Bastineitor73/Biped-Robot/Software y Comunicación/README.md

# Software B1P0

## Rutina principal
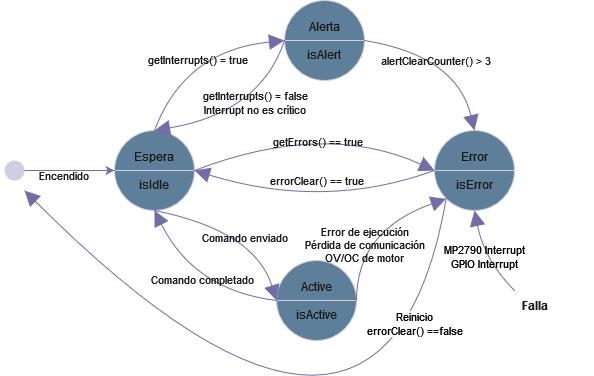
[picture p78: Software y Comunicación/Diagrama_FSM.drawio.png]


## Libreria MP2790
- 144 Direcciones en #define
- 597 Registros en Namespace::MP2790_Reg con tipo struct RegDes
- 24 Metodos publicos
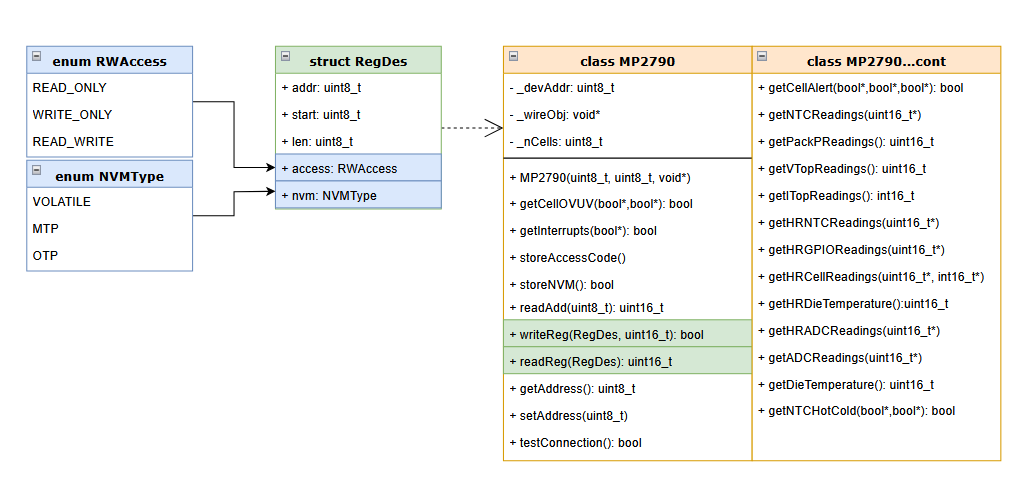
[picture p79: Software y Comunicación/Librerías Arduino/MP27XX/mp2790_class.png]
