Bastineitor73/Biped-Robot/Electrónica/PCB/Prototype1.0/Captura de pantalla 2025-07-23 153957.png

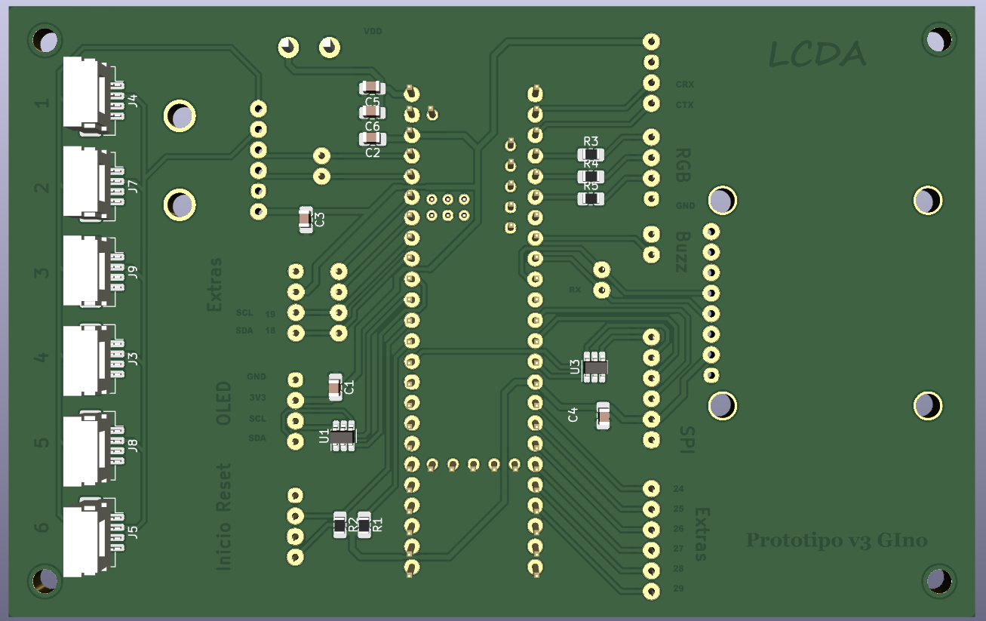
Electrónica/PCB/Prototype1.0/Captura de pantalla 2025-07-23 153957.png
