Bastineitor73/Biped-Robot/invitacion_1.jpg

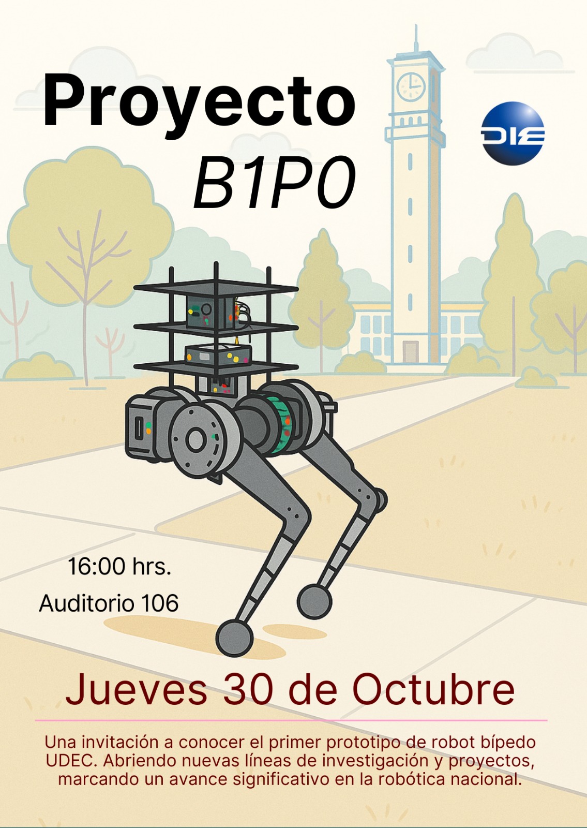
invitacion_1.jpg
