Bastineitor73/Biped-Robot/invitacion_2.png

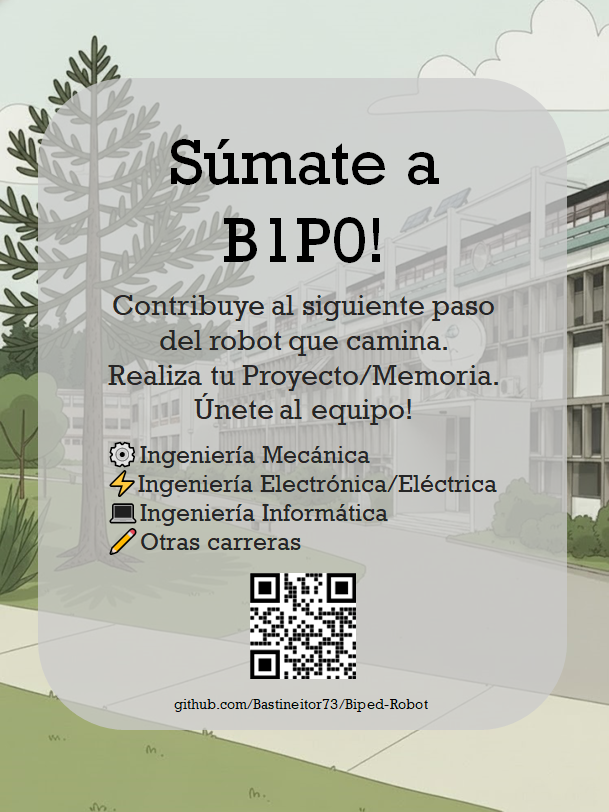
invitacion_2.png
