Bastineitor73/Biped-Robot/Software y Comunicación/Cámara/librealsense/doc/img/ds5_branches.png

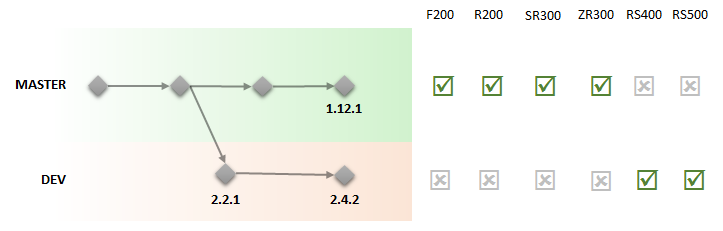
Software y Comunicación/Cámara/librealsense/doc/img/ds5_branches.png
