Bastineitor73/Biped-Robot/Software y Comunicación/Cámara/librealsense/doc/img/LRS_CS_axis_base.png

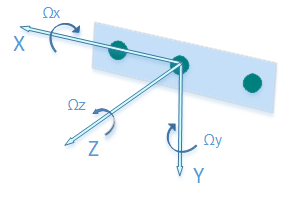
Software y Comunicación/Cámara/librealsense/doc/img/LRS_CS_axis_base.png
