Bastineitor73/Biped-Robot/Software y Comunicación/Cámara/librealsense/doc/img/matlab_select.png

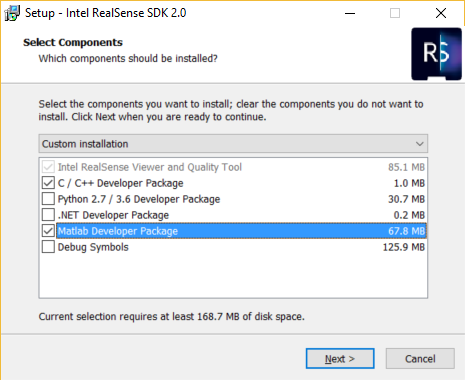
Software y Comunicación/Cámara/librealsense/doc/img/matlab_select.png
