Bastineitor73/Biped-Robot/Software y Comunicación/Cámara/librealsense/doc/img/playback/playback-flow.png

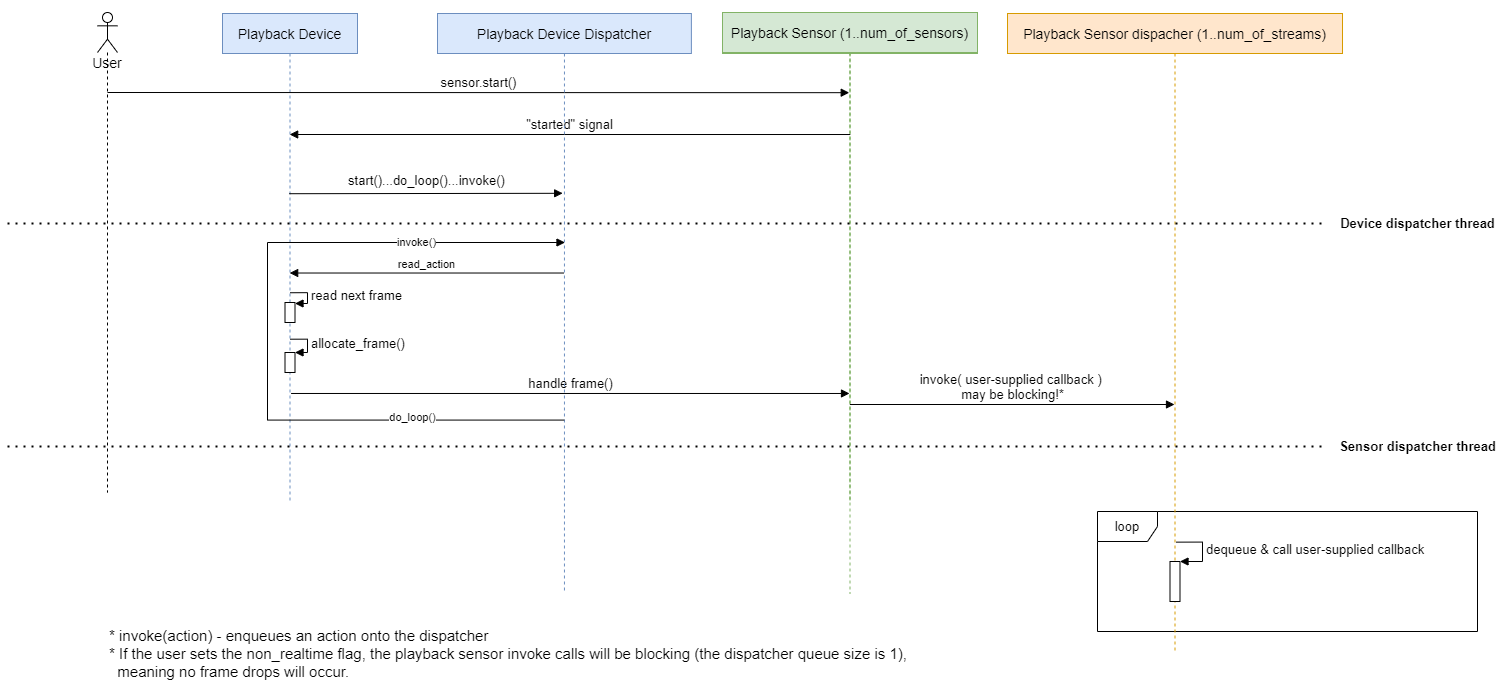
Software y Comunicación/Cámara/librealsense/doc/img/playback/playback-flow.png
