Bastineitor73/Biped-Robot/Software y Comunicación/Cámara/librealsense/doc/img/playback_screenshot.png

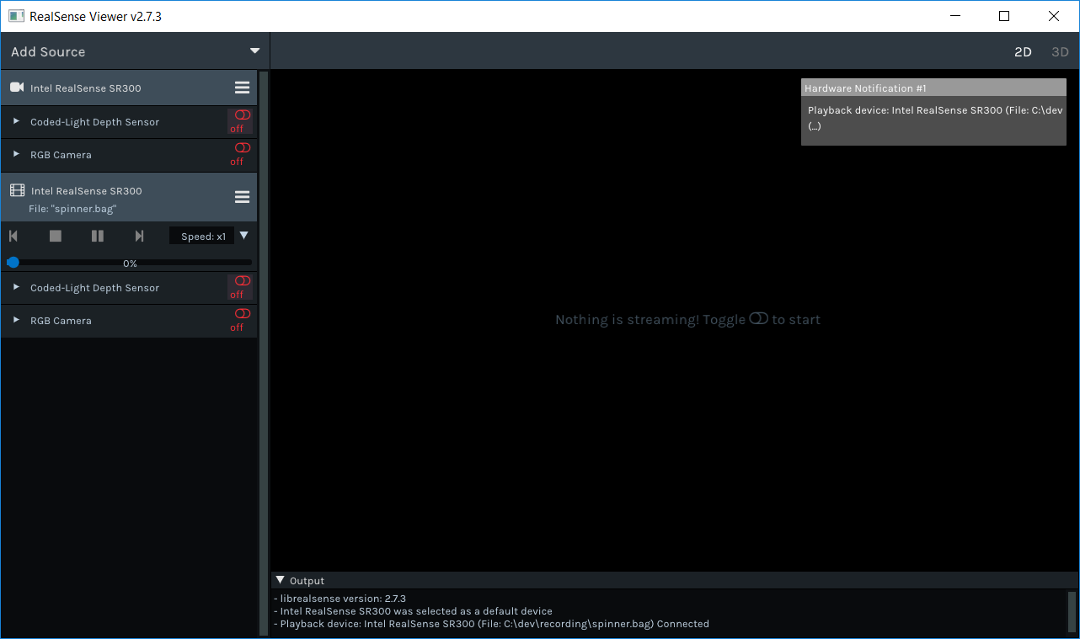
Software y Comunicación/Cámara/librealsense/doc/img/playback_screenshot.png
