Bastineitor73/Biped-Robot/Software y Comunicación/Cámara/librealsense/doc/img/realsense-android.png

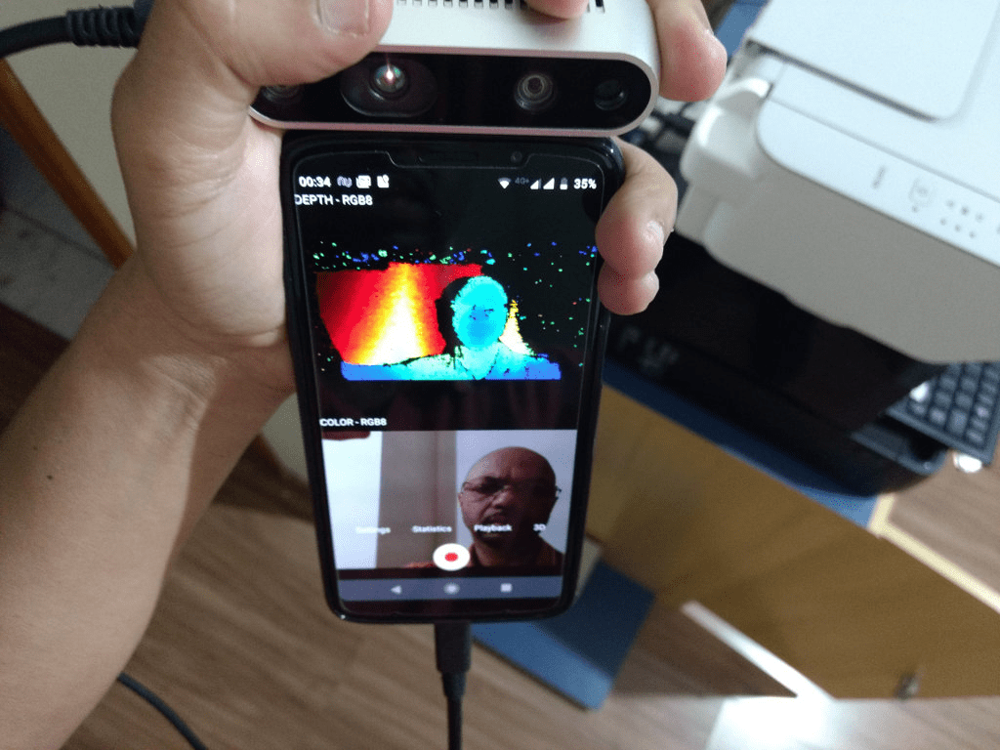
Software y Comunicación/Cámara/librealsense/doc/img/realsense-android.png
