Bastineitor73/Biped-Robot/Software y Comunicación/Cámara/librealsense/doc/img/record_screenshot.png

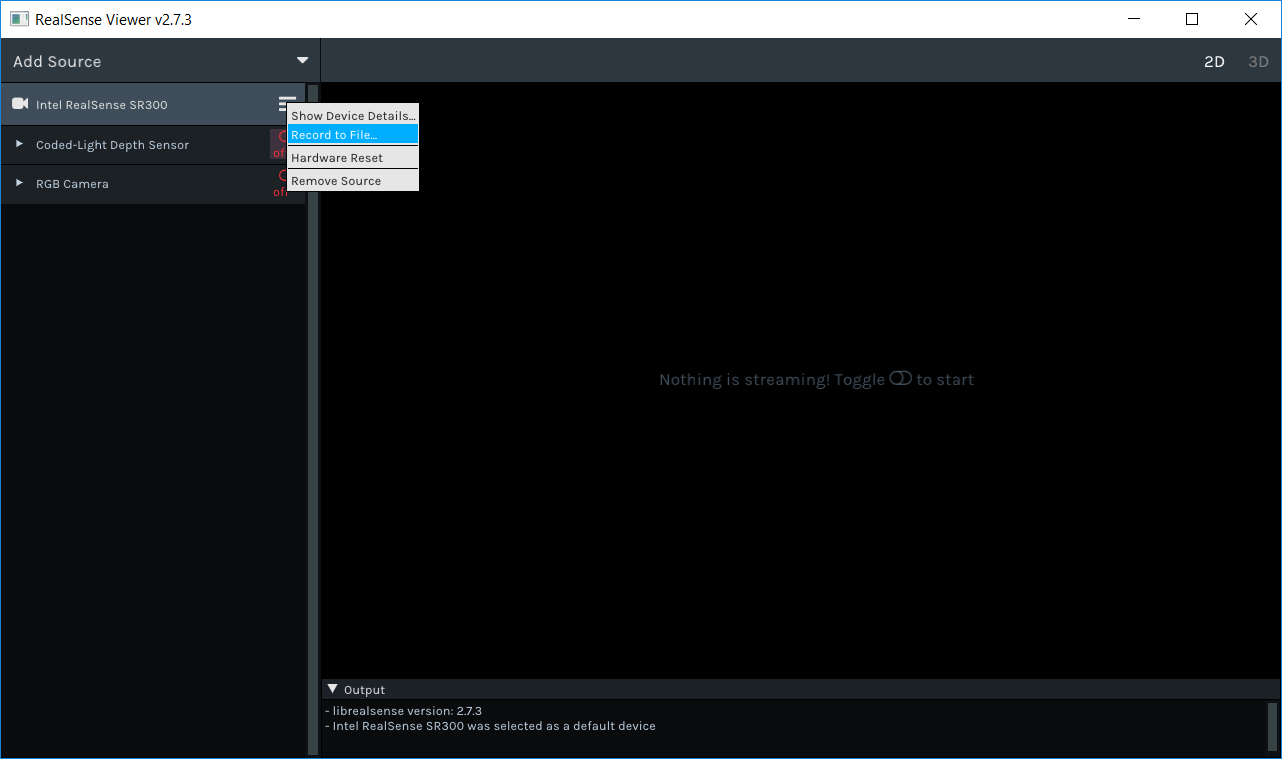
Software y Comunicación/Cámara/librealsense/doc/img/record_screenshot.png
