Bastineitor73/Biped-Robot/Software y Comunicación/Cámara/librealsense/doc/img/sensors_within_device.png

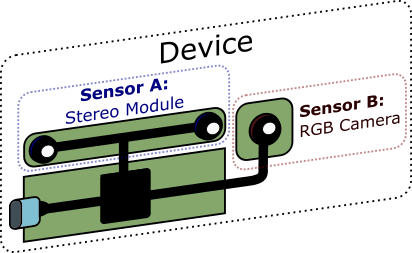
Software y Comunicación/Cámara/librealsense/doc/img/sensors_within_device.png
