Bastineitor73/Biped-Robot/Software y Comunicación/Cámara/librealsense/doc/img/T265_orientation_axis.png

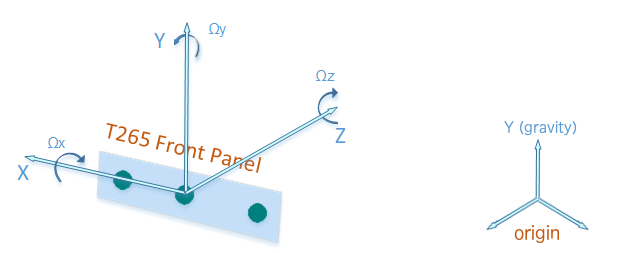
Software y Comunicación/Cámara/librealsense/doc/img/T265_orientation_axis.png
