Bastineitor73/Biped-Robot/Software y Comunicación/Cámara/librealsense/doc/img/T265_Robot1.png

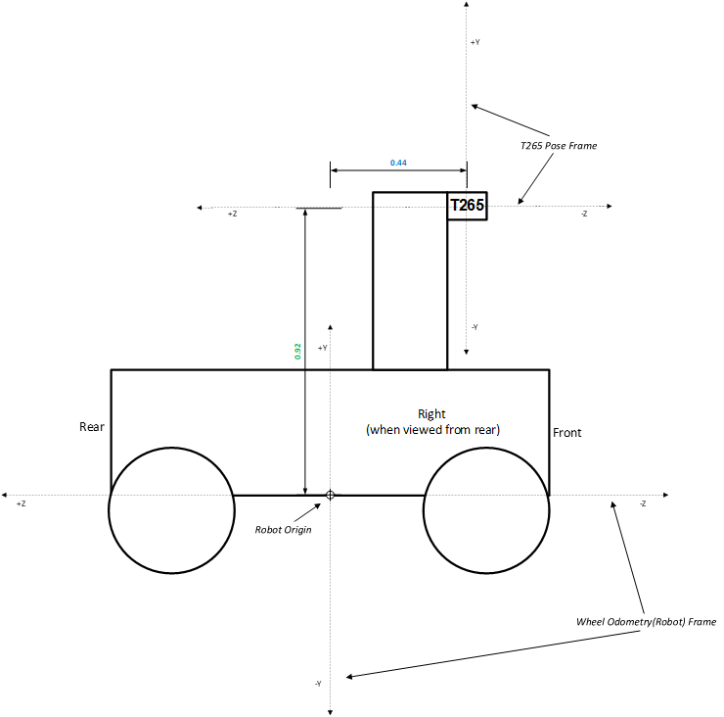
Software y Comunicación/Cámara/librealsense/doc/img/T265_Robot1.png
