Bastineitor73/Biped-Robot/Software y Comunicación/Cámara/librealsense/doc/img/T265_sensor_extrinsics.png

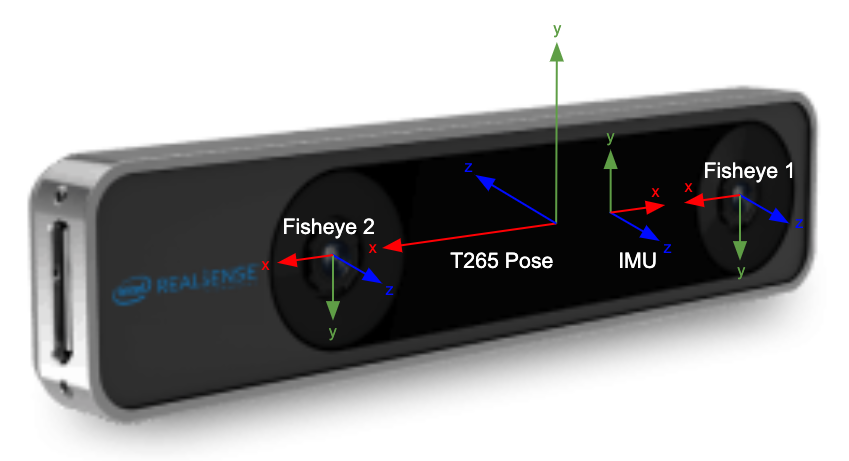
Software y Comunicación/Cámara/librealsense/doc/img/T265_sensor_extrinsics.png
