Bastineitor73/Biped-Robot/Software y Comunicación/Cámara/librealsense/doc/img/updates/updates.png

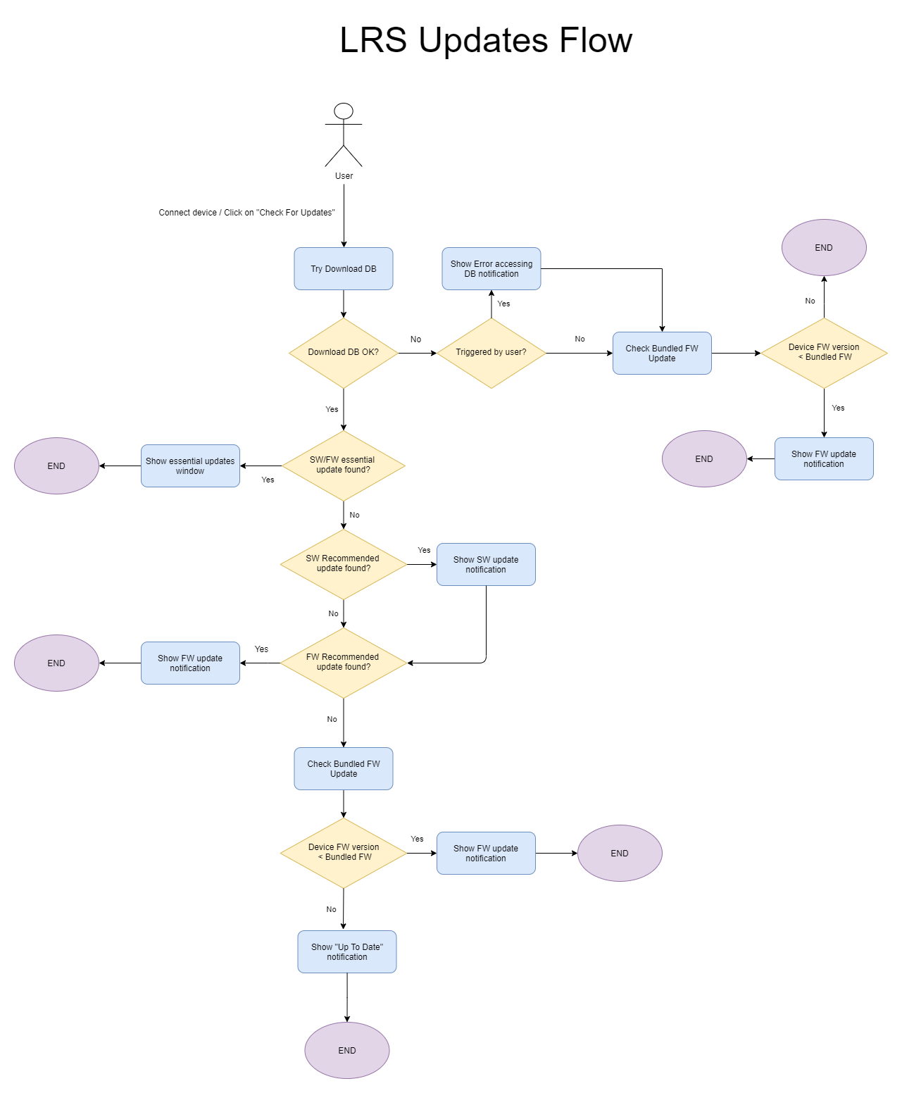
Software y Comunicación/Cámara/librealsense/doc/img/updates/updates.png
