Bastineitor73/Biped-Robot/Software y Comunicación/Cámara/librealsense/doc/img/win_samples.PNG

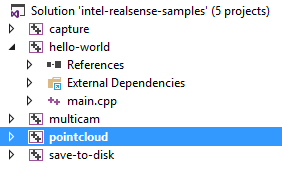
Software y Comunicación/Cámara/librealsense/doc/img/win_samples.PNG
