Bastineitor73/Biped-Robot/Software y Comunicación/Cámara/librealsense/doc/img/win_shortcuts.PNG

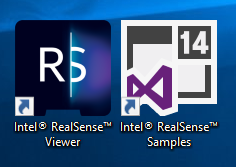
Software y Comunicación/Cámara/librealsense/doc/img/win_shortcuts.PNG
