Bastineitor73/Biped-Robot/Software y Comunicación/Cámara/librealsense/doc/img/windows_pointcloud_preview.PNG

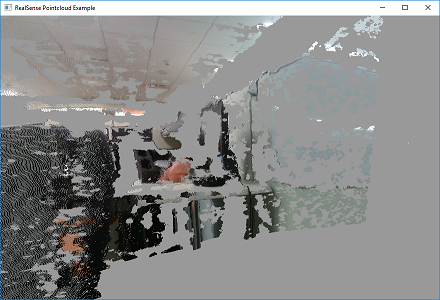
Software y Comunicación/Cámara/librealsense/doc/img/windows_pointcloud_preview.PNG
