Bastineitor73/Biped-Robot/Software y Comunicación/Cámara/librealsense/doc/img/windows_viewer_preview.PNG

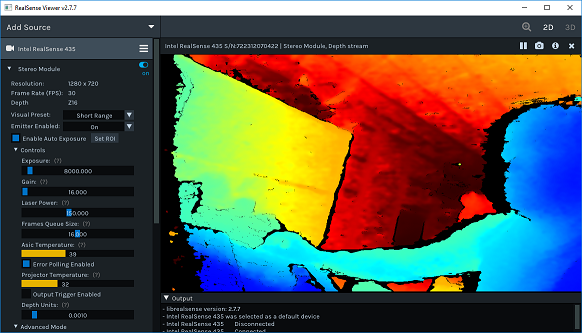
Software y Comunicación/Cámara/librealsense/doc/img/windows_viewer_preview.PNG
