Bastineitor73/Biped-Robot/Software y Comunicación/Cámara/librealsense/doc/metadata/metadata-cpp-config-ui.png

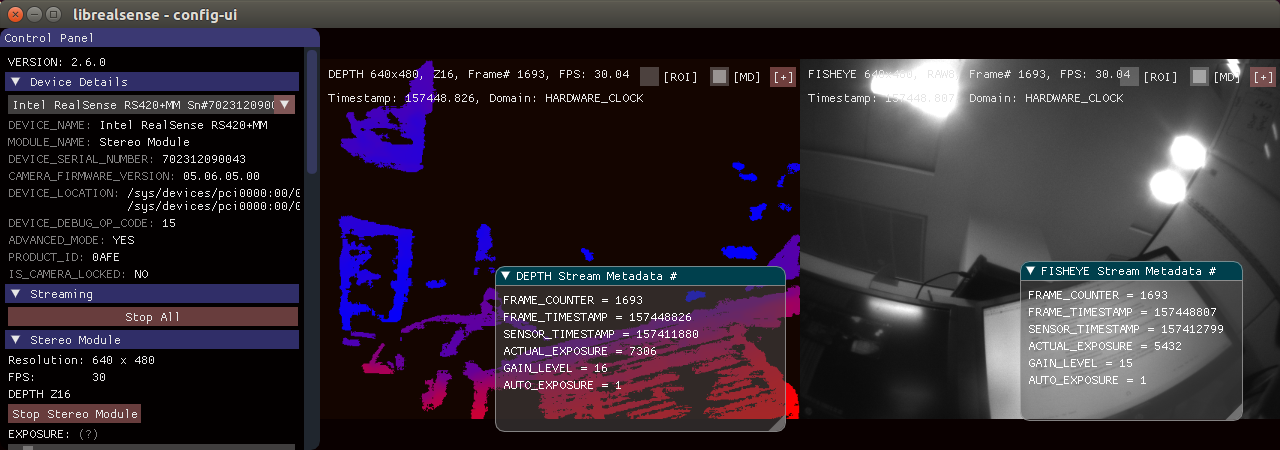
Software y Comunicación/Cámara/librealsense/doc/metadata/metadata-cpp-config-ui.png
