Bastineitor73/Biped-Robot/Software y Comunicación/Cámara/librealsense/doc/metadata/metadata_acquisition_flow.bmp

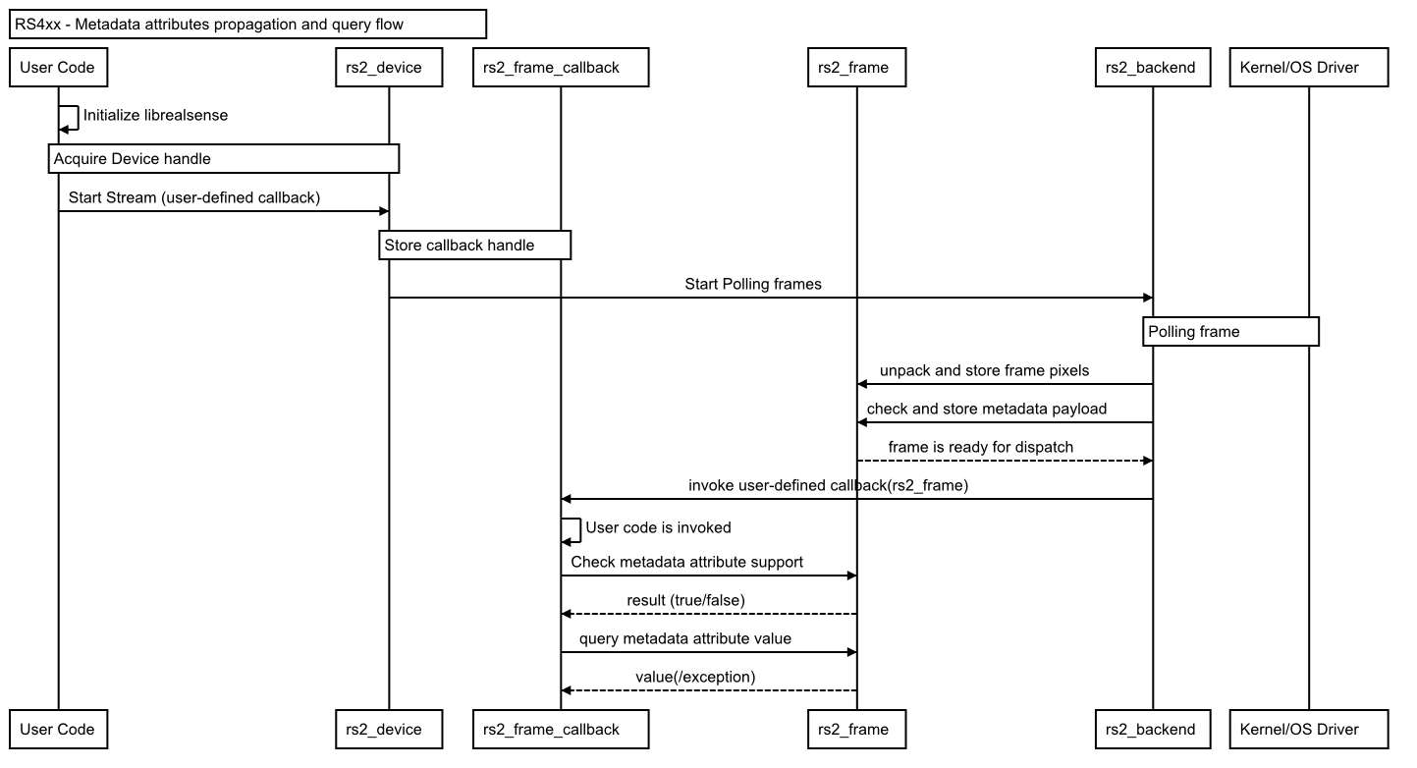
Software y Comunicación/Cámara/librealsense/doc/metadata/metadata_acquisition_flow.bmp
