Bastineitor73/Biped-Robot/Software y Comunicación/Cámara/librealsense/doc/metadata/metadata_registration_flow.bmp

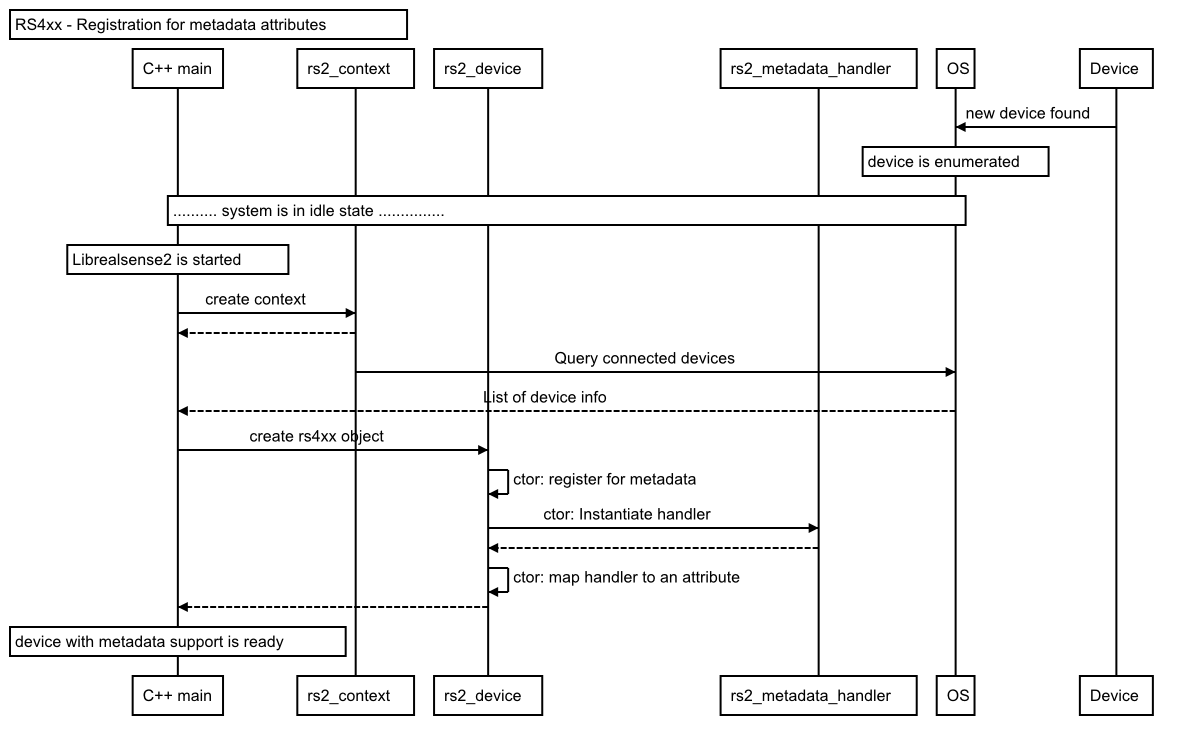
Software y Comunicación/Cámara/librealsense/doc/metadata/metadata_registration_flow.bmp
