Bastineitor73/Biped-Robot/Software y Comunicación/Cámara/librealsense/doc/rs400/advanced_mode_sample.png

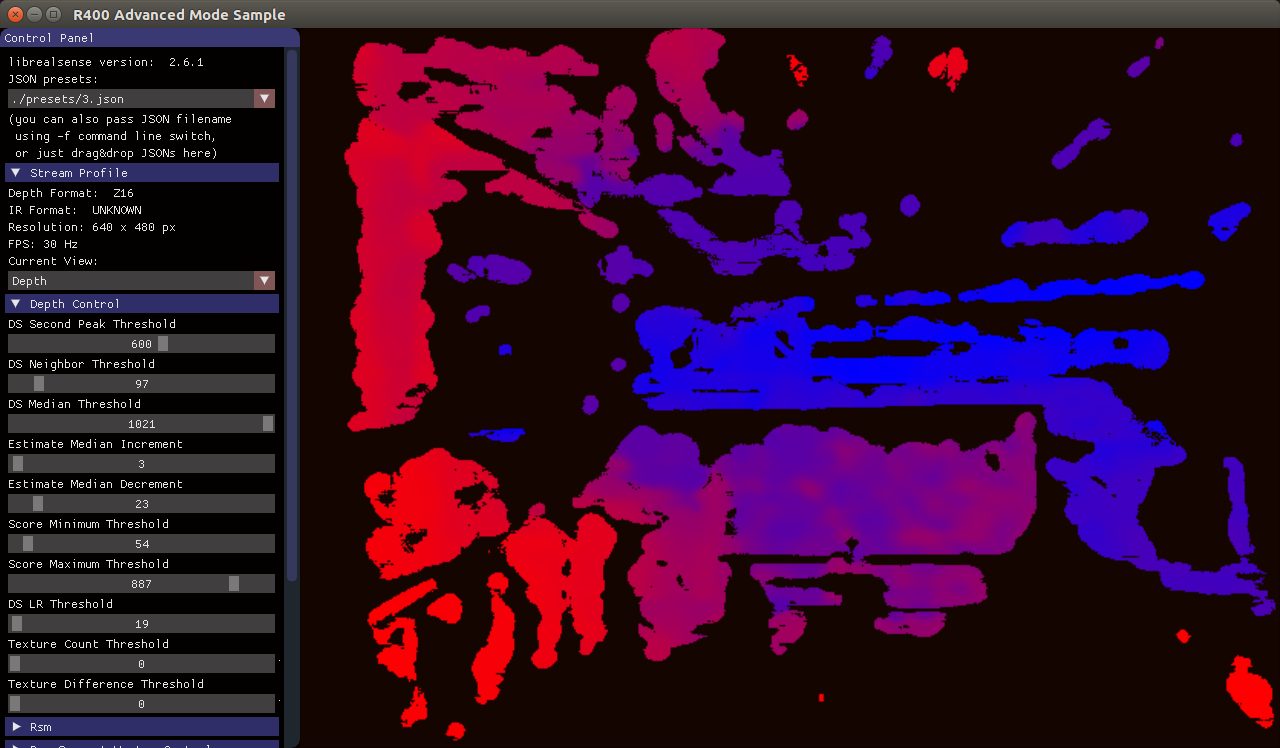
Software y Comunicación/Cámara/librealsense/doc/rs400/advanced_mode_sample.png
