Bastineitor73/Biped-Robot/Software y Comunicación/Cámara/librealsense/doc/stepbystep/resources/Image_Depth.png

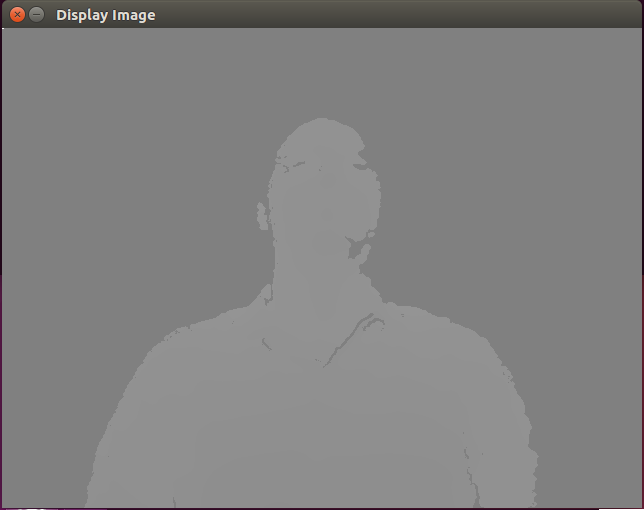
Software y Comunicación/Cámara/librealsense/doc/stepbystep/resources/Image_Depth.png
