Bastineitor73/Biped-Robot/Software y Comunicación/Cámara/librealsense/doc/stepbystep/resources/Image_IR-noColorMap.png

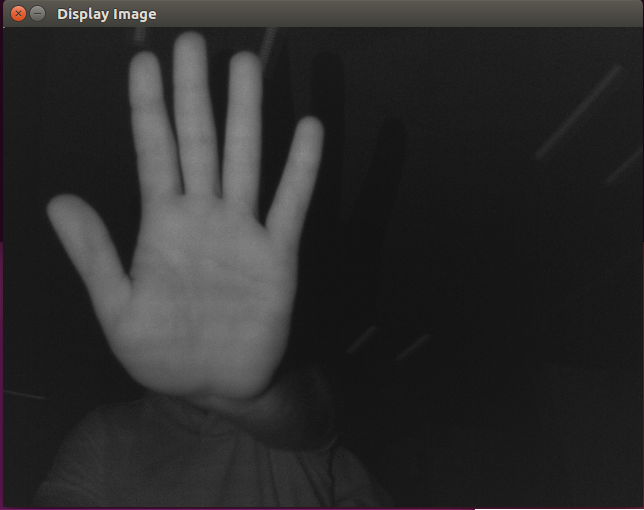
Software y Comunicación/Cámara/librealsense/doc/stepbystep/resources/Image_IR-noColorMap.png
