Bastineitor73/Biped-Robot/Software y Comunicación/Cámara/librealsense/examples/gl/output.PNG

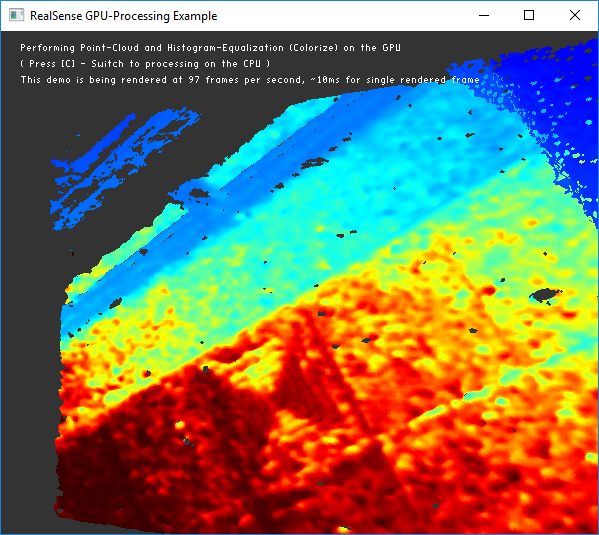
Software y Comunicación/Cámara/librealsense/examples/gl/output.PNG
