Bastineitor73/Biped-Robot/Software y Comunicación/Cámara/librealsense/scripts/Docker/LRS_Docker_Depth_example.gif

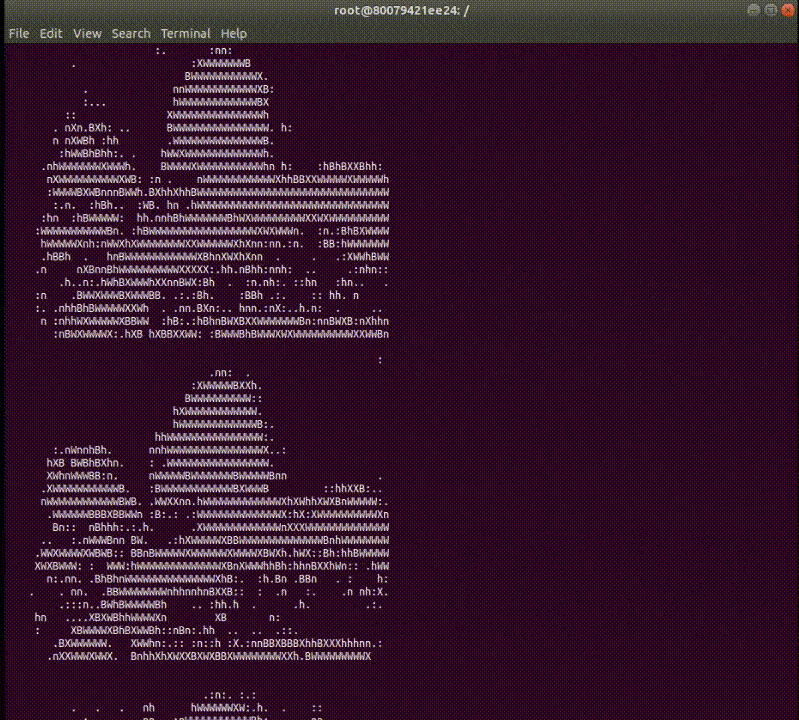
Software y Comunicación/Cámara/librealsense/scripts/Docker/LRS_Docker_Depth_example.gif
