Bastineitor73/Biped-Robot/Software y Comunicación/Cámara/librealsense/tools/depth-quality/res/z_accuracy.png

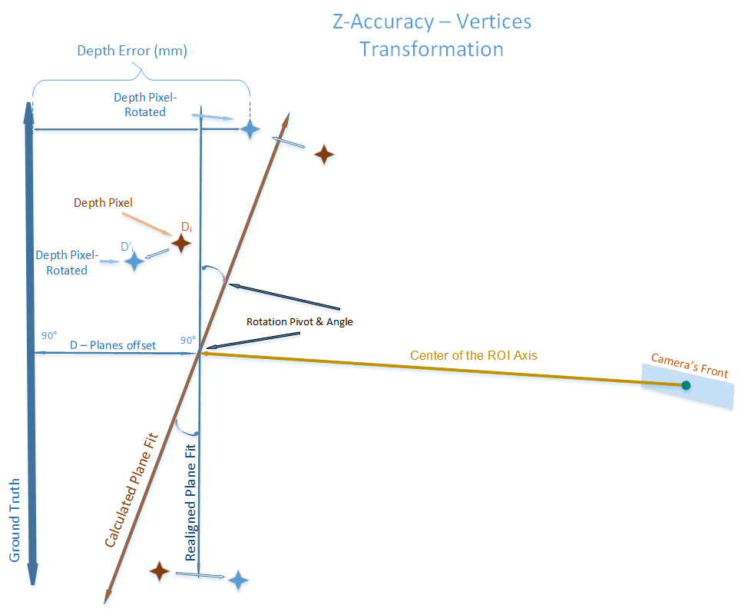
Software y Comunicación/Cámara/librealsense/tools/depth-quality/res/z_accuracy.png
