Bastineitor73/Biped-Robot/Software y Comunicación/Cámara/librealsense/tools/depth-quality/res/Zi_ZPi.png

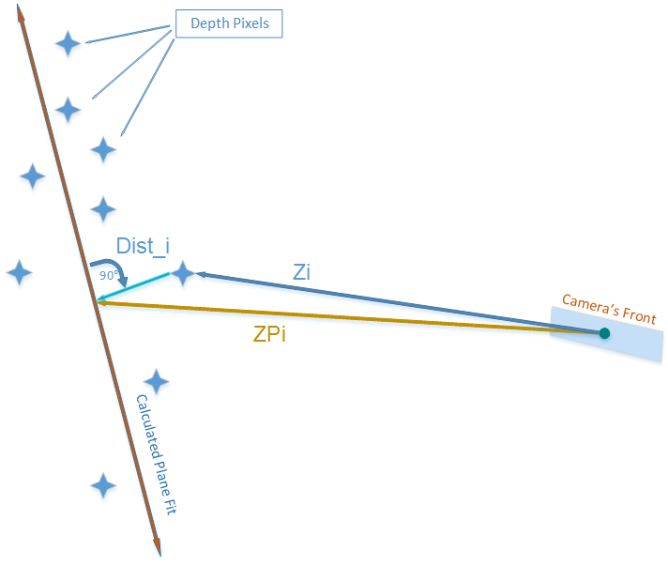
Software y Comunicación/Cámara/librealsense/tools/depth-quality/res/Zi_ZPi.png
