Bastineitor73/Biped-Robot/Software y Comunicación/Cámara/librealsense/wrappers/dlib/face/rs-face-dlib.jpg

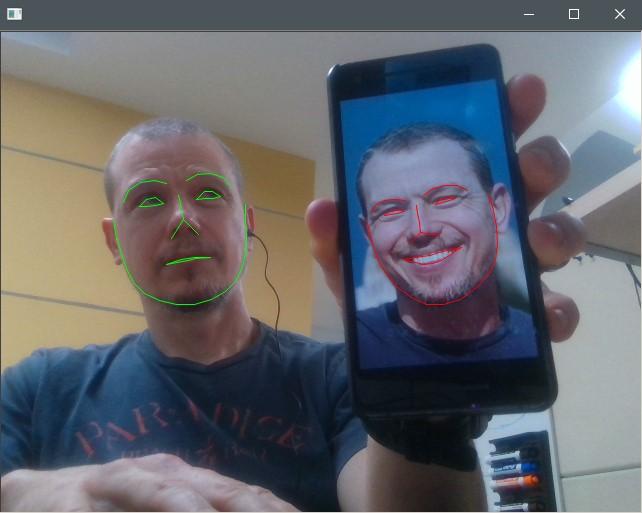
Software y Comunicación/Cámara/librealsense/wrappers/dlib/face/rs-face-dlib.jpg
