Bastineitor73/Biped-Robot/Software y Comunicación/Cámara/librealsense/wrappers/opencv/dnn/res/1.PNG

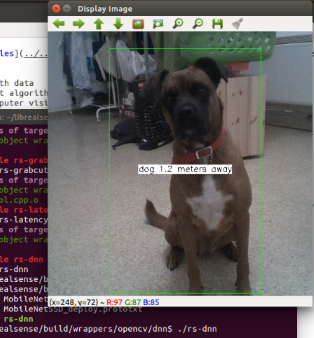
Software y Comunicación/Cámara/librealsense/wrappers/opencv/dnn/res/1.PNG
