Bastineitor73/Biped-Robot/Software y Comunicación/Cámara/librealsense/wrappers/opencv/grabcuts/res/input.png

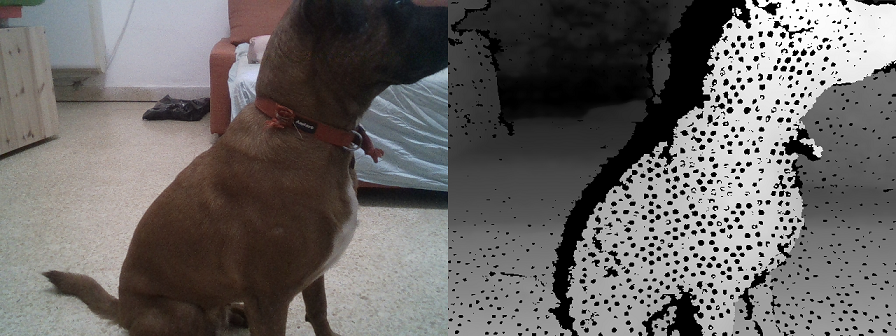
Software y Comunicación/Cámara/librealsense/wrappers/opencv/grabcuts/res/input.png
