Bastineitor73/Biped-Robot/Software y Comunicación/Cámara/librealsense/wrappers/opencv/grabcuts/res/masks.png

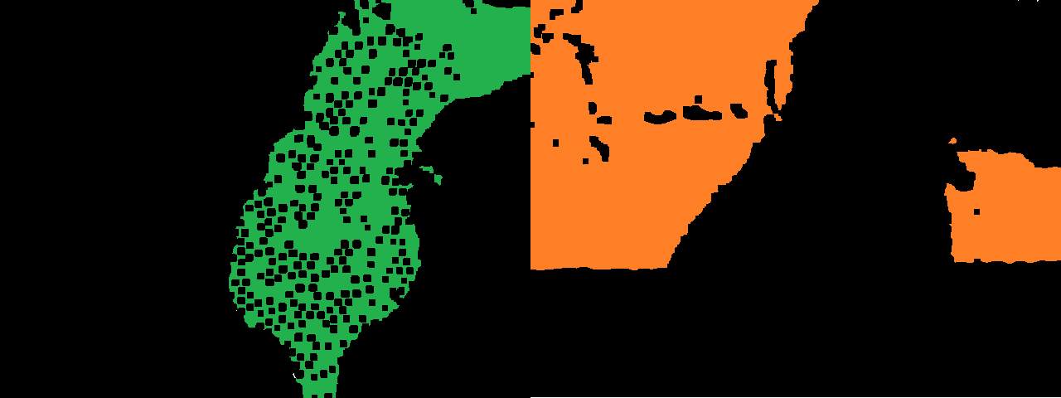
Software y Comunicación/Cámara/librealsense/wrappers/opencv/grabcuts/res/masks.png
