Bastineitor73/Biped-Robot/Software y Comunicación/Cámara/librealsense/wrappers/opencv/latency-tool/res/3.png

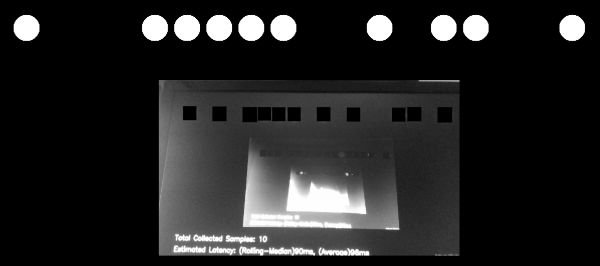
Software y Comunicación/Cámara/librealsense/wrappers/opencv/latency-tool/res/3.png
