Bastineitor73/Biped-Robot/Software y Comunicación/Cámara/librealsense/wrappers/opencv/res/4.PNG

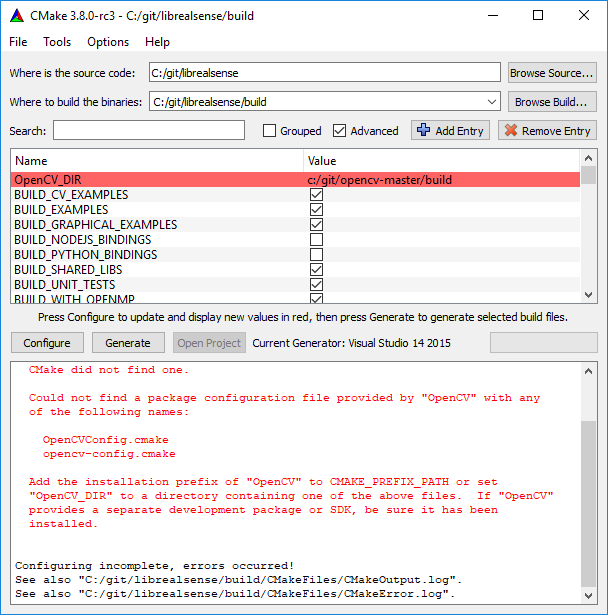
Software y Comunicación/Cámara/librealsense/wrappers/opencv/res/4.PNG
