Bastineitor73/Biped-Robot/Software y Comunicación/Cámara/librealsense/wrappers/opencv/rotate-pointcloud/res/front.png

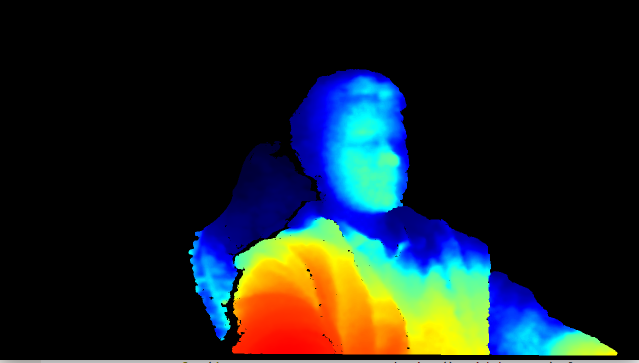
Software y Comunicación/Cámara/librealsense/wrappers/opencv/rotate-pointcloud/res/front.png
