Bastineitor73/Biped-Robot/Software y Comunicación/Cámara/librealsense/wrappers/opencv/rotate-pointcloud/res/roll_90.png

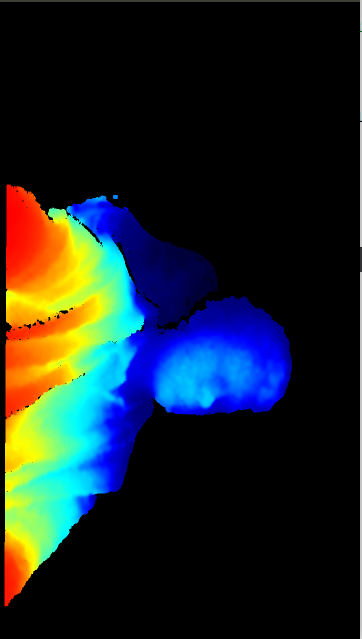
Software y Comunicación/Cámara/librealsense/wrappers/opencv/rotate-pointcloud/res/roll_90.png
