Bastineitor73/Biped-Robot/Software y Comunicación/Cámara/librealsense/wrappers/opencv/rotate-pointcloud/res/yaw_90.png

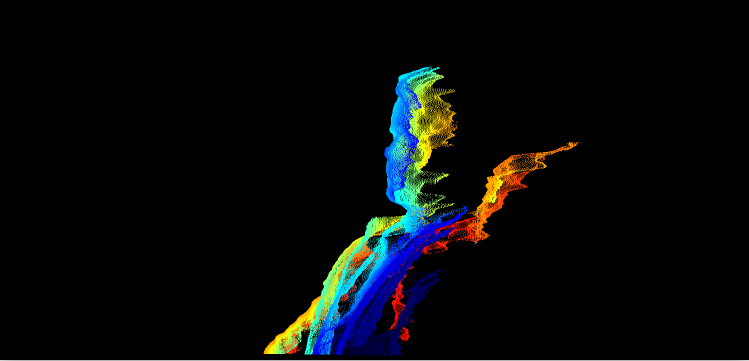
Software y Comunicación/Cámara/librealsense/wrappers/opencv/rotate-pointcloud/res/yaw_90.png
