Bastineitor73/Biped-Robot/Software y Comunicación/Cámara/librealsense/wrappers/openni2/doc/img/demo.jpg

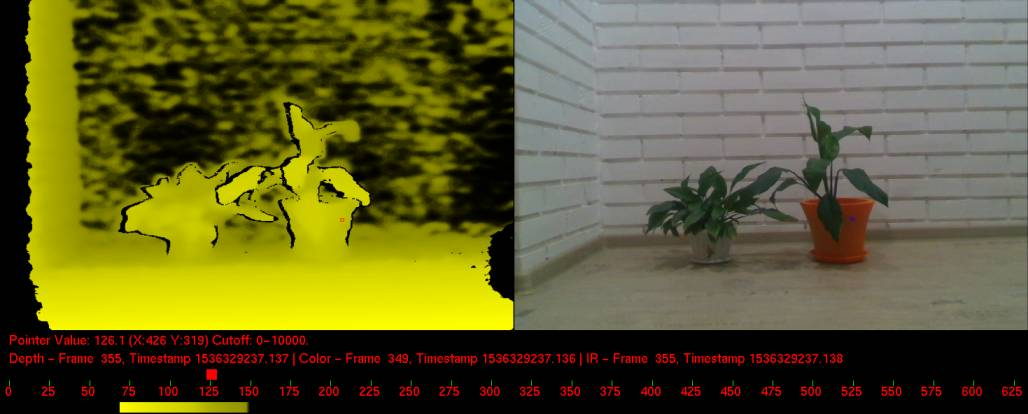
Software y Comunicación/Cámara/librealsense/wrappers/openni2/doc/img/demo.jpg
