Bastineitor73/Biped-Robot/Software y Comunicación/Cámara/librealsense/wrappers/openni2/doc/img/oni_capture.jpg

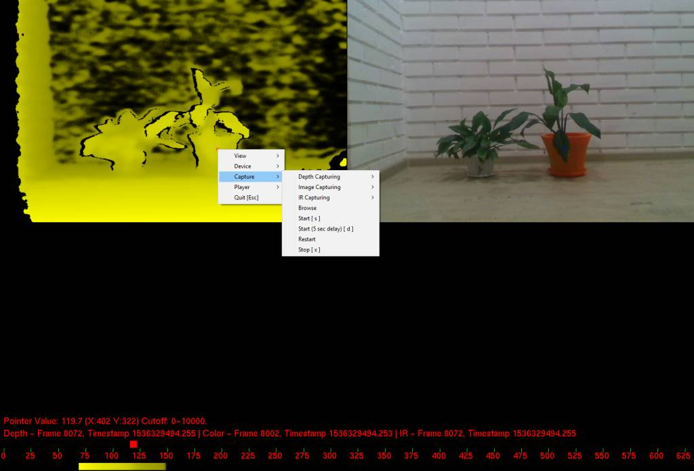
Software y Comunicación/Cámara/librealsense/wrappers/openni2/doc/img/oni_capture.jpg
