Bastineitor73/Biped-Robot/Software y Comunicación/Cámara/librealsense/wrappers/openvino/dnn/rs-dnn-vino.jpg

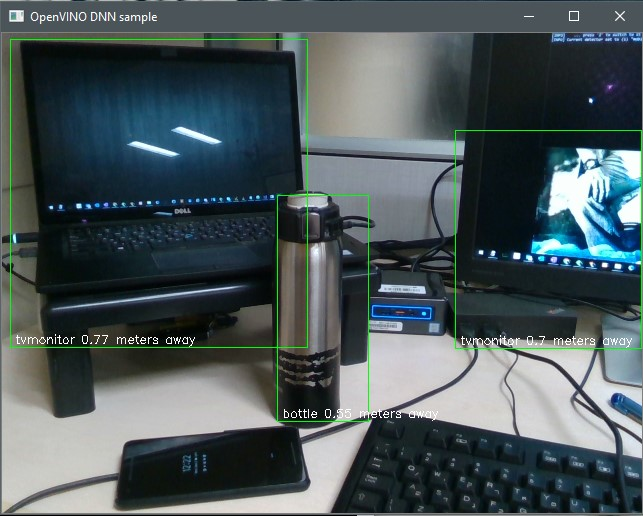
Software y Comunicación/Cámara/librealsense/wrappers/openvino/dnn/rs-dnn-vino.jpg
