Bastineitor73/Biped-Robot/Software y Comunicación/Cámara/librealsense/wrappers/openvino/face/rs-face-vino.jpg

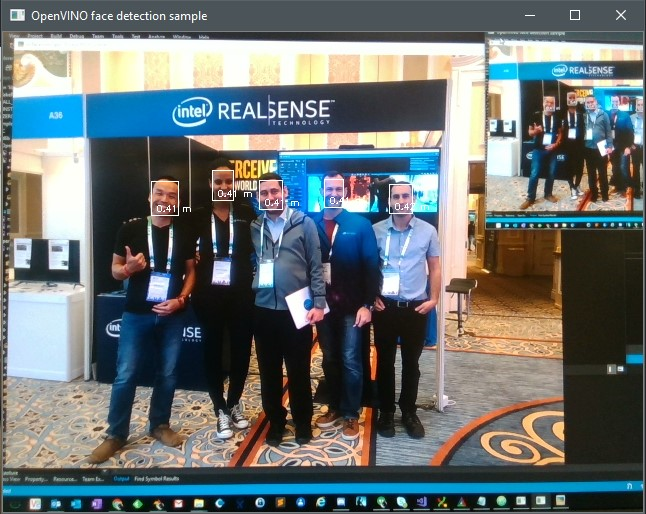
Software y Comunicación/Cámara/librealsense/wrappers/openvino/face/rs-face-vino.jpg
