Bastineitor73/Biped-Robot/Software y Comunicación/Cámara/librealsense/wrappers/pcl/res/1.PNG

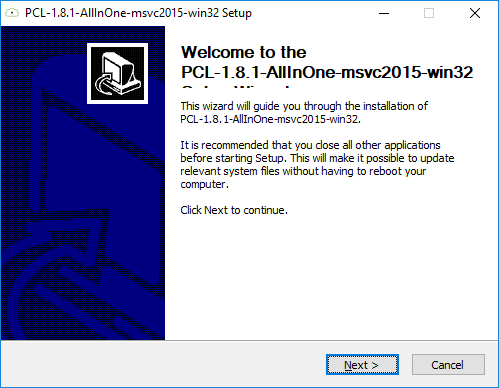
Software y Comunicación/Cámara/librealsense/wrappers/pcl/res/1.PNG
