Bastineitor73/Biped-Robot/Software y Comunicación/Cámara/librealsense/wrappers/python/examples/ethernet_client_server/MultiCameraEthernet.png

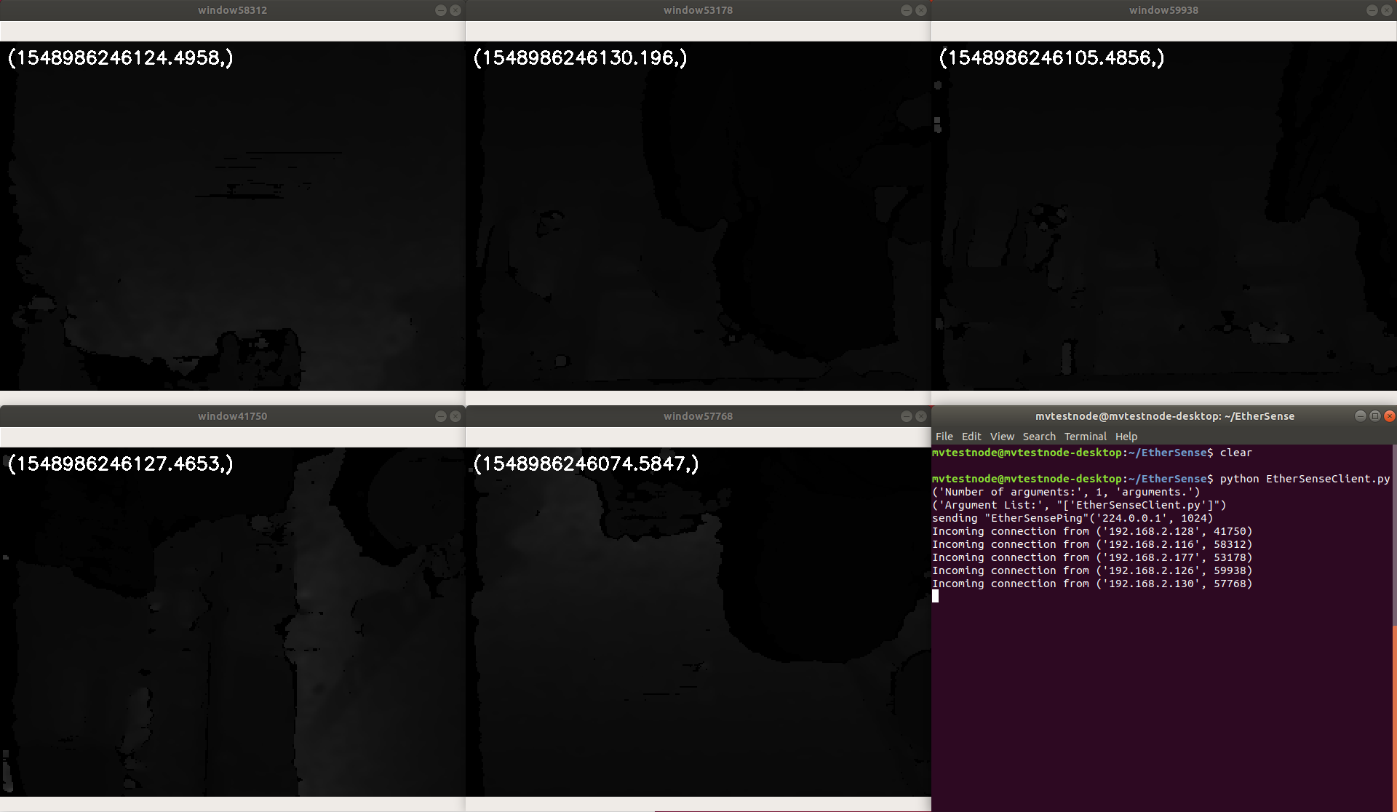
Software y Comunicación/Cámara/librealsense/wrappers/python/examples/ethernet_client_server/MultiCameraEthernet.png
