Bastineitor73/Biped-Robot/Software y Comunicación/Cámara/librealsense/wrappers/tensorflow/images/conver_to_bag.PNG

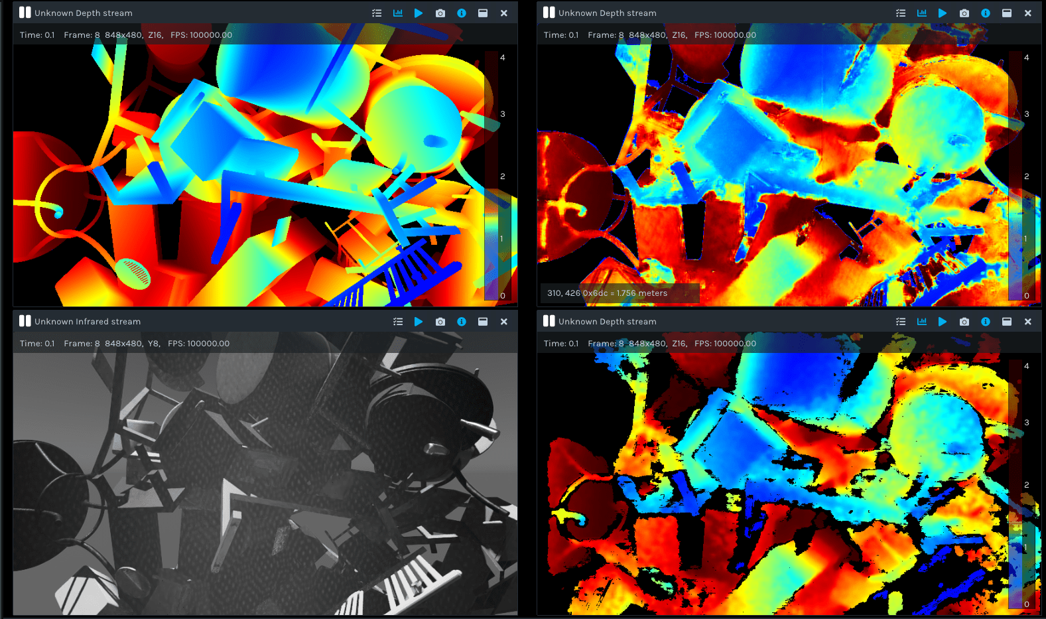
Software y Comunicación/Cámara/librealsense/wrappers/tensorflow/images/conver_to_bag.PNG
