Bastineitor73/Biped-Robot/Software y Comunicación/Cámara/librealsense/wrappers/tensorflow/images/example_1.PNG

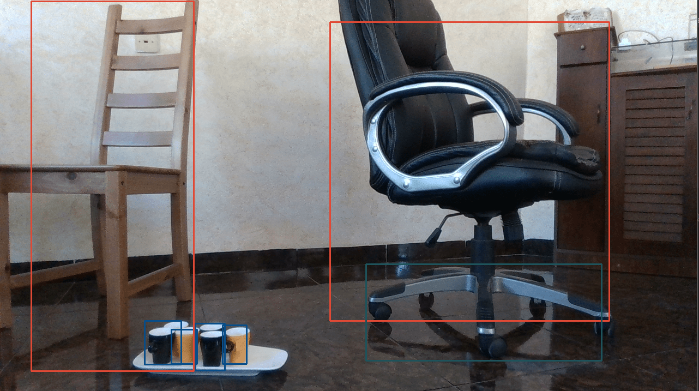
Software y Comunicación/Cámara/librealsense/wrappers/tensorflow/images/example_1.PNG
