Bastineitor73/Biped-Robot/Software y Comunicación/Cámara/librealsense/wrappers/tensorflow/images/example_2.PNG

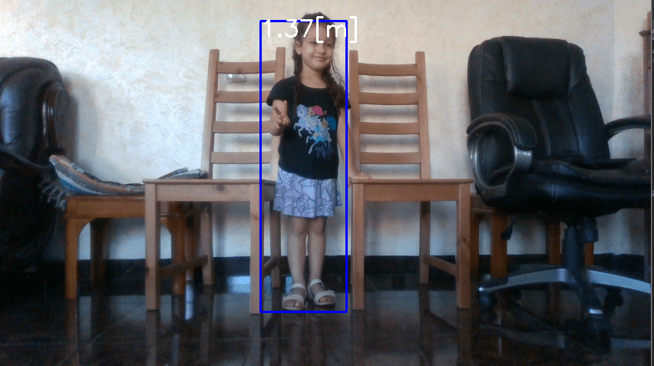
Software y Comunicación/Cámara/librealsense/wrappers/tensorflow/images/example_2.PNG
