Bastineitor73/Biped-Robot/Software y Comunicación/Cámara/librealsense/wrappers/tensorflow/images/rmse.PNG

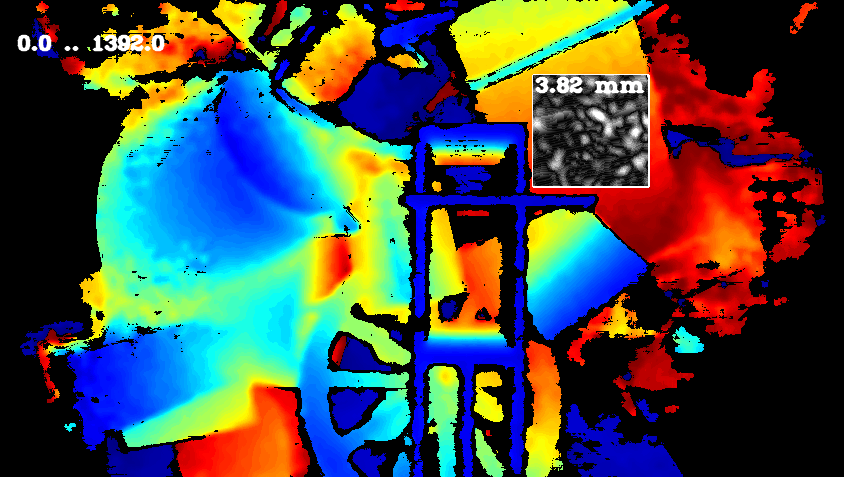
Software y Comunicación/Cámara/librealsense/wrappers/tensorflow/images/rmse.PNG
