Bastineitor73/Biped-Robot/Software y Comunicación/Cámara/librealsense/wrappers/unity/Assets/RealSenseSDK2.0/Misc/Textures/forkme_left_darkblue_121621.png

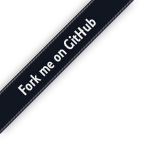
Software y Comunicación/Cámara/librealsense/wrappers/unity/Assets/RealSenseSDK2.0/Misc/Textures/forkme_left_darkblue_121621.png
