Bastineitor73/Biped-Robot/Software y Comunicación/Cámara/librealsense/wrappers/unity/Assets/RealSenseSDK2.0/Misc/Textures/realsense.png

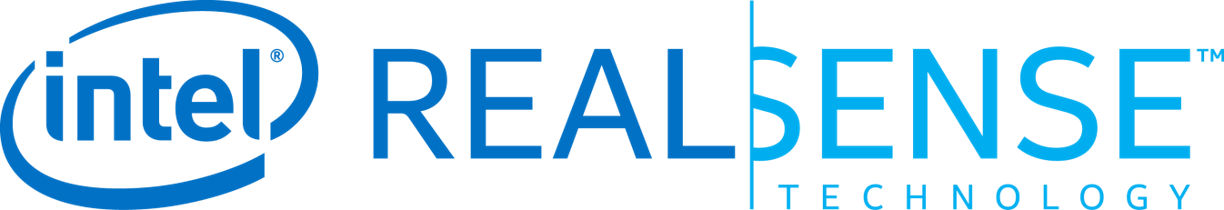
Software y Comunicación/Cámara/librealsense/wrappers/unity/Assets/RealSenseSDK2.0/Misc/Textures/realsense.png
