Bastineitor73/Biped-Robot/Software y Comunicación/Cámara/librealsense/wrappers/unrealengine4/doc/img/bp_enum_devices.jpg

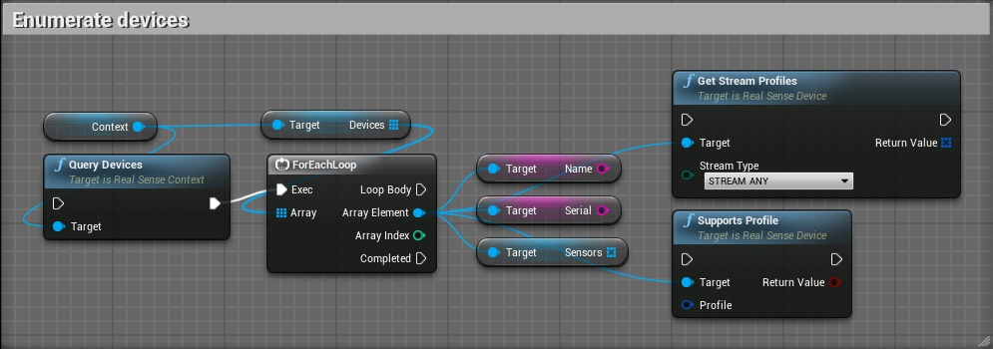
Software y Comunicación/Cámara/librealsense/wrappers/unrealengine4/doc/img/bp_enum_devices.jpg
