Bastineitor73/Biped-Robot/Software y Comunicación/Cámara/librealsense/wrappers/unrealengine4/doc/img/bp_enum_options.jpg

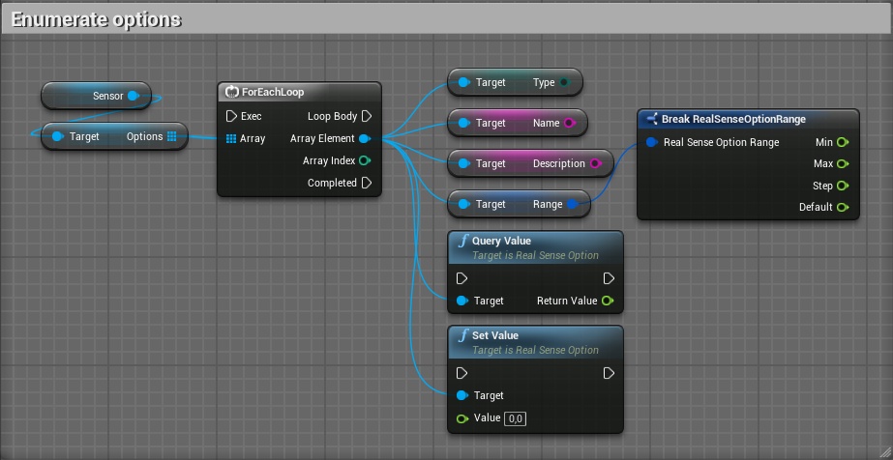
Software y Comunicación/Cámara/librealsense/wrappers/unrealengine4/doc/img/bp_enum_options.jpg
