Bastineitor73/Biped-Robot/Software y Comunicación/Cámara/librealsense/wrappers/unrealengine4/doc/img/bp_get_inspector.jpg

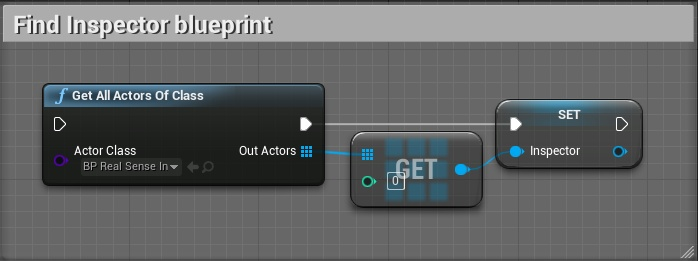
Software y Comunicación/Cámara/librealsense/wrappers/unrealengine4/doc/img/bp_get_inspector.jpg
