Bastineitor73/Biped-Robot/Software y Comunicación/Cámara/librealsense/wrappers/unrealengine4/doc/img/demo.jpg

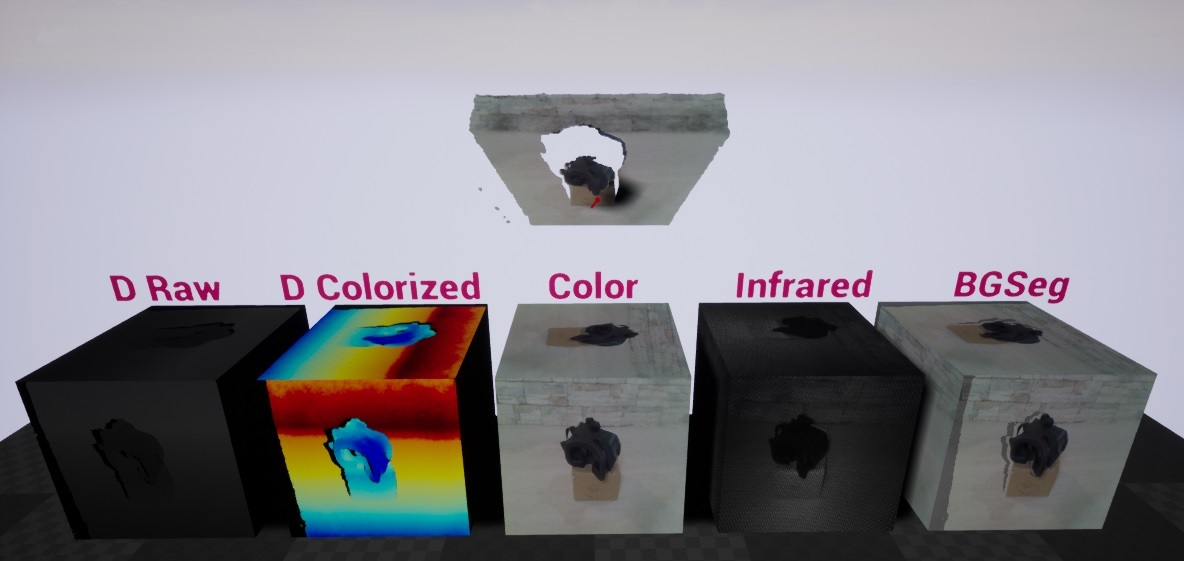
Software y Comunicación/Cámara/librealsense/wrappers/unrealengine4/doc/img/demo.jpg
