Bastineitor73/Biped-Robot/Software y Comunicación/Cámara/librealsense/wrappers/unrealengine4/doc/img/device_dropdown.jpg

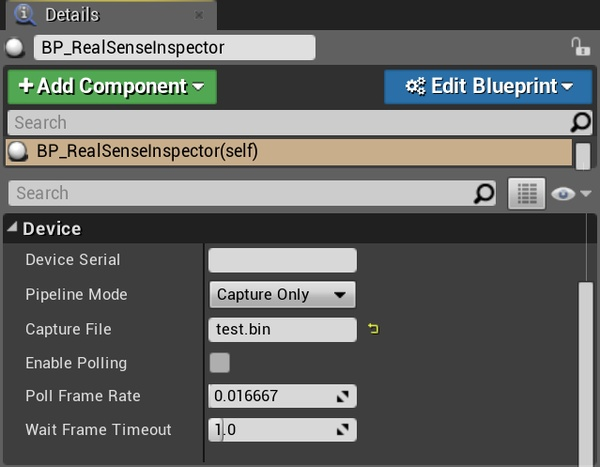
Software y Comunicación/Cámara/librealsense/wrappers/unrealengine4/doc/img/device_dropdown.jpg
