Bastineitor73/Biped-Robot/Software y Comunicación/Cámara/librealsense/wrappers/unrealengine4/doc/img/hw_inspector.jpg

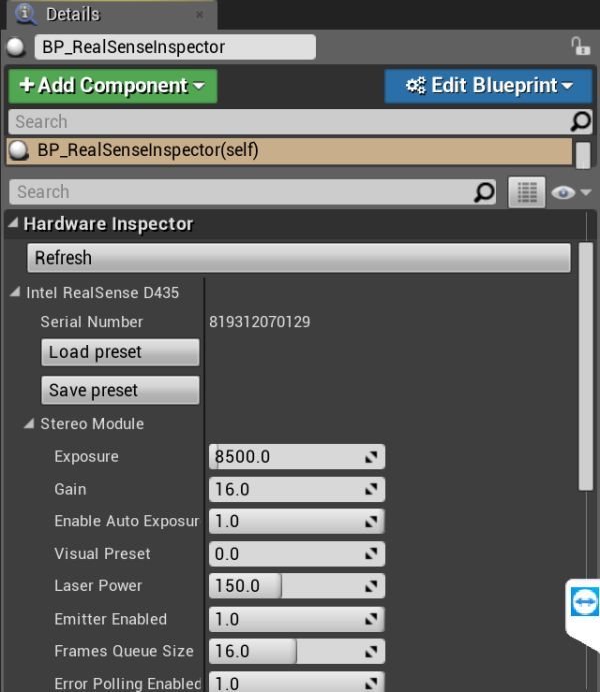
Software y Comunicación/Cámara/librealsense/wrappers/unrealengine4/doc/img/hw_inspector.jpg
