Bastineitor73/Biped-Robot/Software y Comunicación/Cámara/librealsense/wrappers/unrealengine4/doc/img/pcl_config.jpg

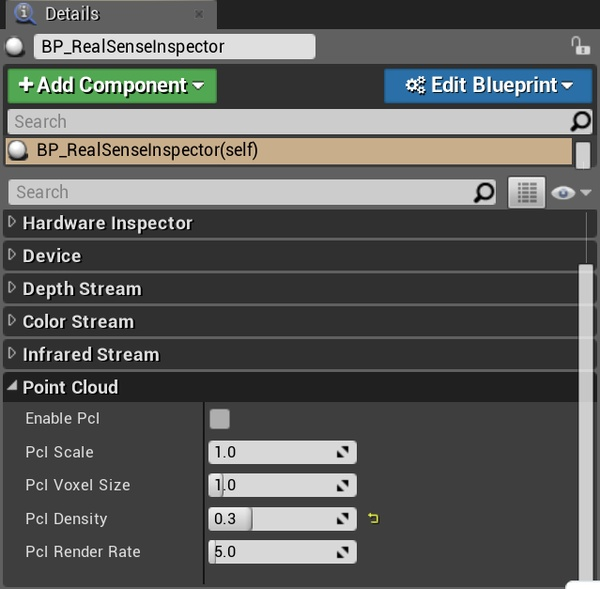
Software y Comunicación/Cámara/librealsense/wrappers/unrealengine4/doc/img/pcl_config.jpg
