Bastineitor73/Biped-Robot/Software y Comunicación/Cámara/librealsense/wrappers/unrealengine4/doc/img/record_playback_ui.jpg

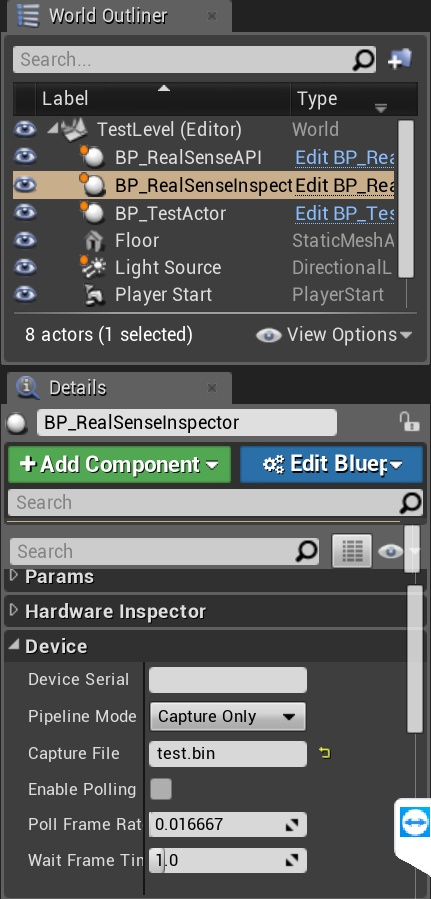
Software y Comunicación/Cámara/librealsense/wrappers/unrealengine4/doc/img/record_playback_ui.jpg
