Bastineitor73/Biped-Robot/Software y Comunicación/Cámara/librealsense/wrappers/python/examples/box_dimensioner_multicam/samplesetupandoutput.jpg

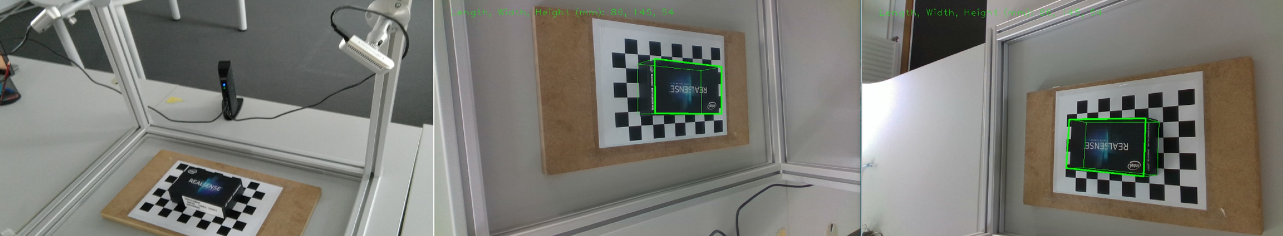
Software y Comunicación/Cámara/librealsense/wrappers/python/examples/box_dimensioner_multicam/samplesetupandoutput.jpg
