Bastineitor73/Biped-Robot/Software y Comunicación/Cámara/librealsense/tools/rs-imu-calibration/images/IMG_4918.jpg

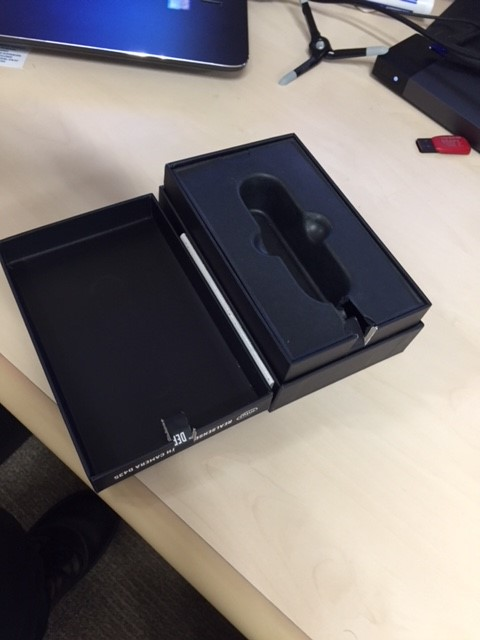
Software y Comunicación/Cámara/librealsense/tools/rs-imu-calibration/images/IMG_4918.jpg
