Bastineitor73/Biped-Robot/Software y Comunicación/Cámara/librealsense/tools/rs-imu-calibration/images/IMG_4921.JPG

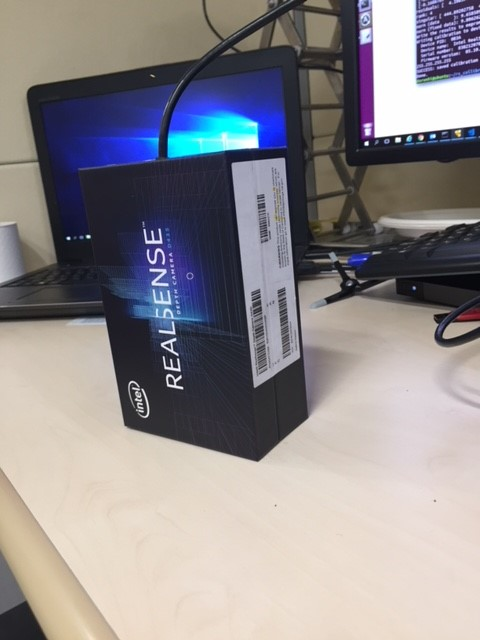
Software y Comunicación/Cámara/librealsense/tools/rs-imu-calibration/images/IMG_4921.JPG
