Bastineitor73/Biped-Robot/Software y Comunicación/Cámara/librealsense/wrappers/opencv/kinfu/res/result.gif

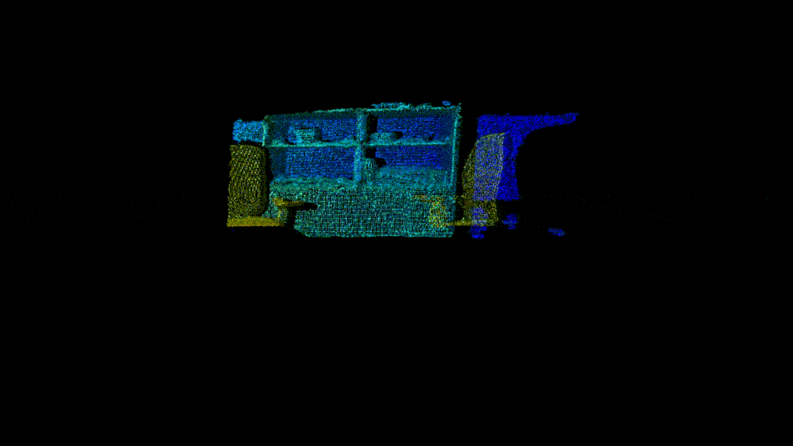
Software y Comunicación/Cámara/librealsense/wrappers/opencv/kinfu/res/result.gif
